williamlorenzen/LoRaWAN-Team/gui_software/checkmark.jpg

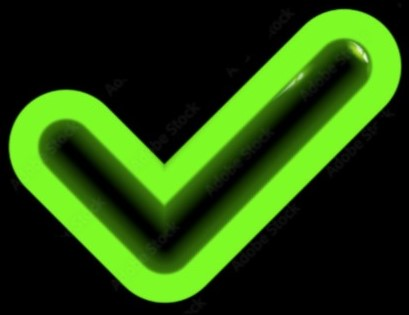
gui_software/checkmark.jpg
