williamlorenzen/LoRaWAN-Team/gui_software/warning.jpg

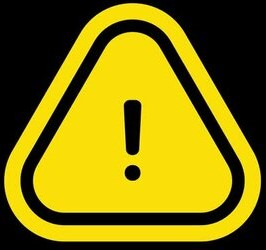
gui_software/warning.jpg
